dariusbbl/OpenBook/Images/Display.png

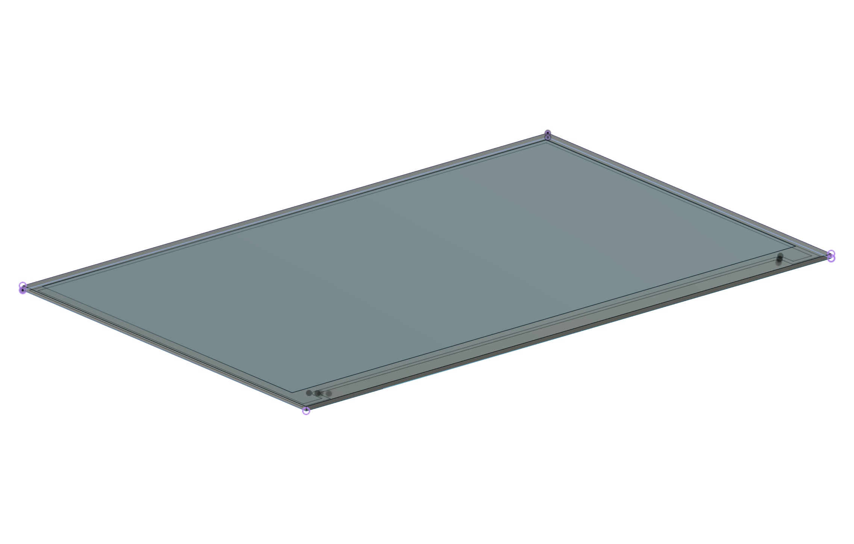
Images/Display.png
