dariusbbl/OpenBook/Images/OpenBookInside.png

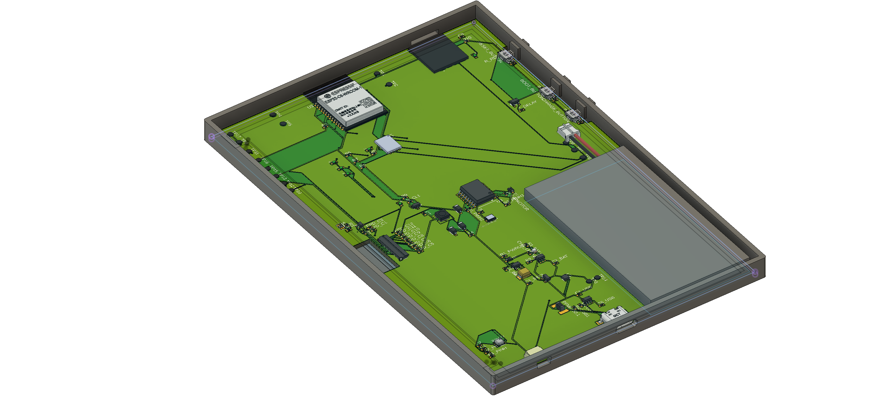
Images/OpenBookInside.png
