dariusbbl/OpenBook/Images/Components.png

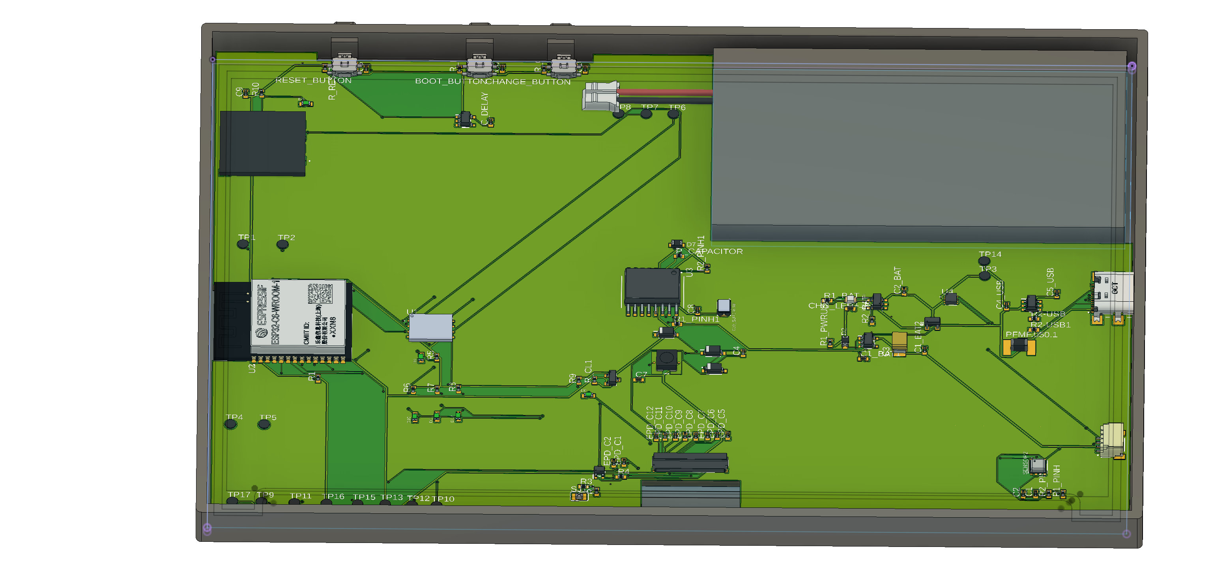
Images/Components.png
